tampueduard/luce/img/prefboard-1.png

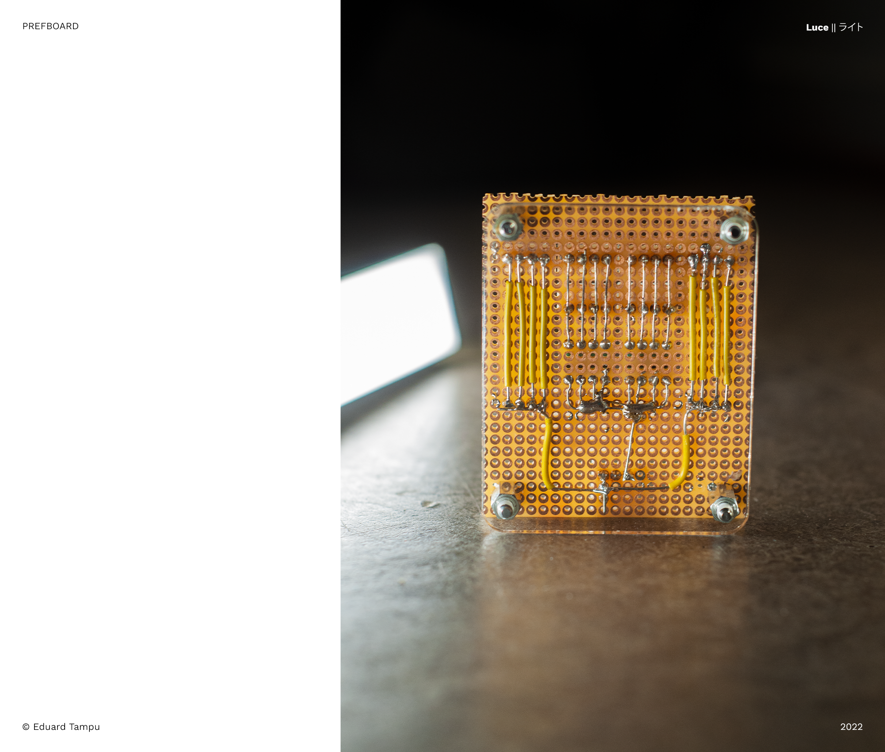
img/prefboard-1.png
